maxim75/cc1101_receiver_esp32/include/secrets.example.h

#pragma once

// Copy this file to include/secrets.h (gitignored) and fill in your values.

#define WIFI_SSID       "your-ssid"
#define WIFI_PASSWORD   "your-wifi-password"

#define MQTT_HOST       "192.168.1.10"
#define MQTT_PORT       1883
#define MQTT_USER       "your-mqtt-user"
#define MQTT_PASSWORD   "your-mqtt-password"
